ktjauki/Environmental-Brain-Cube/Media/Setup On Perfboard.JPG

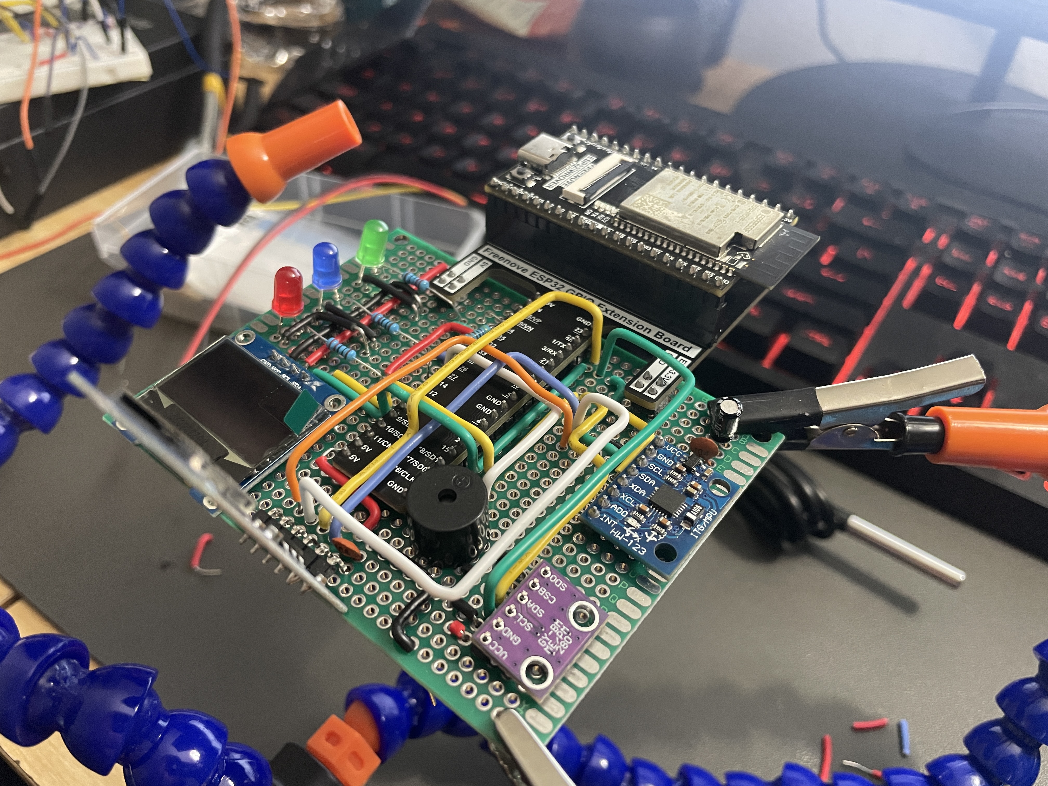
Media/Setup On Perfboard.JPG
