ktjauki/Environmental-Brain-Cube/Media/Soldered flip side of voltage divider.JPG

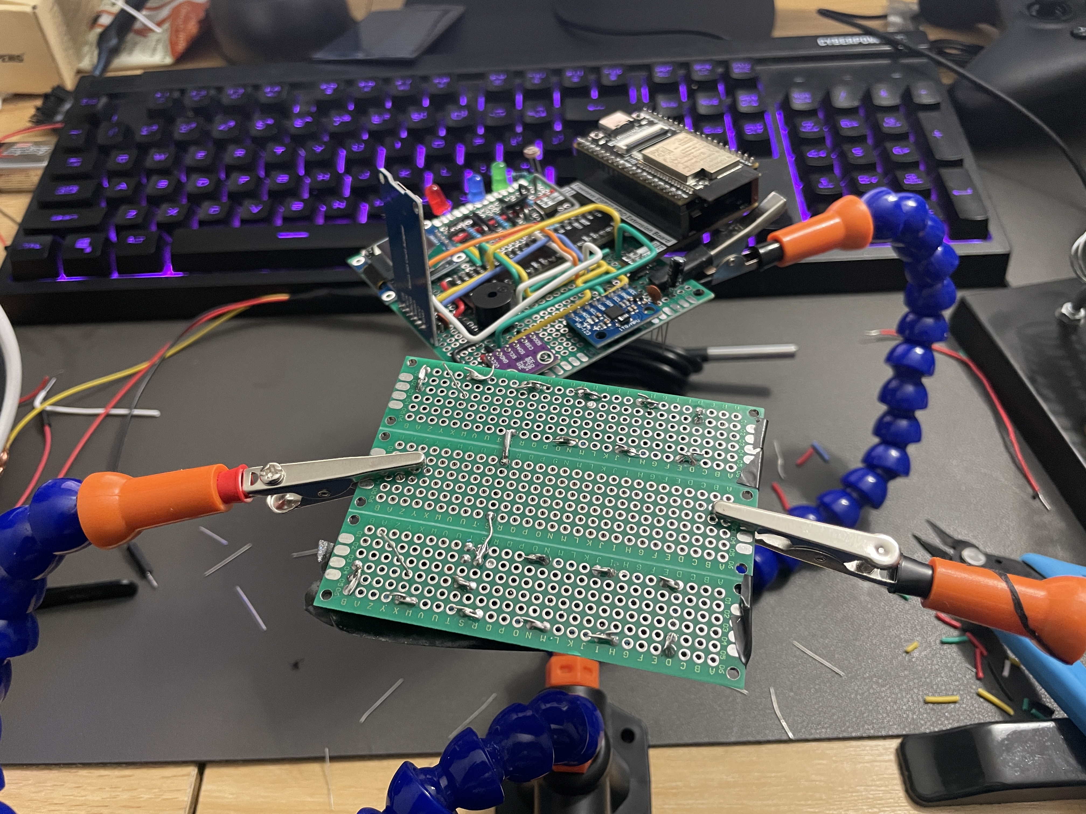
Media/Soldered flip side of voltage divider.JPG
